minmos/terrasense/firmware/components/sys_utils/include/sys_led.h

// components/sys_utils/include/sys_led.h
#pragma once

#include "esp_err.h"
#include "hal/gpio_types.h"
#include "led_strip.h"
#include "freertos/FreeRTOS.h"
#include "freertos/task.h"

// Either GRB or RGB, using GRB if SYS_LED_COLOR_ORDER_GRB is set
#define SYS_LED_COLOR_ORDER_GRB 1

#define GPIO_BUILTIN_LED    8
#define BUILTIN_LED_COUNT   1

// define if we want to add some LED debuggin for componenents
#define SYS_LED_DEBUG_NETWORK_EN    1  
#define SYS_LED_DEBUG_SENSOR_EN     1  
#define SYS_LED_DEBUG_ACTOR_EN      1
#define SYS_PED_DEBUG_APP_LOGIC_EN  1
#if SYS_LED_DEBUG_NETWORK_EN
    #define LED_NOTIFY_NET(led, blinks)     sys_led_notify(led, LED_COLOR_BLUE, blinks)
#else
    #define LED_NOTIFY_NET(led, blinks)     do {} while(0)
#endif
// --- Sensor Diagnostics ---
#if SYS_LED_DEBUG_SENSOR_EN
    #define LED_NOTIFY_SENSOR(led, blinks)  sys_led_notify(led, LED_COLOR_CYAN, blinks)
#else
    #define LED_NOTIFY_SENSOR(led, blinks)  do {} while(0)
#endif
// --- Actor Diagnostics ---
#if SYS_LED_DEBUG_ACTOR_EN
    #define LED_NOTIFY_ACTOR(led, blinks)   sys_led_notify(led, LED_COLOR_WHITE, blinks)
#else
    #define LED_NOTIFY_ACTOR(led, blinks)   do {} while(0)
#endif
// --- App logic Diagnostics ---
#if SYS_PED_DEBUG_APP_LOGIC_EN
    #define LED_NOTIFY_APP_LOGIC(led, blinks)   sys_led_notify(led, LED_COLOR_WHITE, blinks)
#else
    #define LED_NOTIFY_APP_LOGIC(led, blinks)   do {} while(0)
#endif

typedef struct {
    uint8_t r;
    uint8_t g;
    uint8_t b;
} sys_led_color_t;

#if(SYS_LED_COLOR_ORDER_GRB)
    #define MAKE_COLOR(red, green, blue) (sys_led_color_t){ .r = (green), .g = (red), .b = (blue) }
#else
    #define MAKE_COLOR(red, green, blue) (sys_led_color_t){ .r = (red), .g = (green), .b = (blue) }
#endif

// --- Color Definitions using RGB ---
#define LED_COLOR_YELLOW MAKE_COLOR(255, 180, 0)
#define LED_COLOR_ORANGE MAKE_COLOR(255, 80,  0)
#define LED_COLOR_GREEN  MAKE_COLOR(0,   255, 0)
#define LED_COLOR_CYAN   MAKE_COLOR(0,   255, 255)
#define LED_COLOR_BLUE   MAKE_COLOR(0,   0,   255)
#define LED_COLOR_RED    MAKE_COLOR(255, 0,   0)
#define LED_COLOR_PURPLE MAKE_COLOR(255, 0,   255)
#define LED_COLOR_WHITE  MAKE_COLOR(255, 255, 255)
#define LED_COLOR_BLACK  MAKE_COLOR(0,   0,   0)


// --- Base System States ---
typedef enum {
    SYS_LED_STATE_BOOTING,  
    SYS_LED_STATE_OK_DAY,   
    SYS_LED_STATE_OK_NIGHT, 
    SYS_LED_STATE_ERROR,    
    SYS_LED_STATE_OFF       
} sys_led_state_t;


// --- LED Object Definition ---
typedef struct {
    led_strip_handle_t handle;
    uint16_t num_leds;
    volatile sys_led_state_t current_state; 
    TaskHandle_t task_handle;
    
    volatile uint8_t override_blinks_left;
    volatile bool override_trigger; 
    sys_led_color_t override_color; 
} sys_debug_led_t;


/**
 *  Initializes builtin LED and spawing background task.
 */
esp_err_t sys_led_init(sys_debug_led_t *led_obj);

/**
 *  Changing the long term state of controller 
 */
esp_err_t sys_led_set_state(sys_debug_led_t *led_obj, sys_led_state_t state);

/**
 *  Triggers a transient diagnostic flash interrupting the normal state
 */
esp_err_t sys_led_notify(sys_debug_led_t *led_obj, sys_led_color_t color, uint8_t n_blinks);

/**
 * Only for internal task use only. Using this manually may conflict with the background state machine.
 */
esp_err_t sys_led_set_color(sys_debug_led_t *led_obj, sys_led_color_t color, uint8_t brightness_pct);
